Mecha12RumbaoaOsborne/ME405-TERM-PROJECT/Supplemental files/Lab0x00/5 working mostly/log plot.png

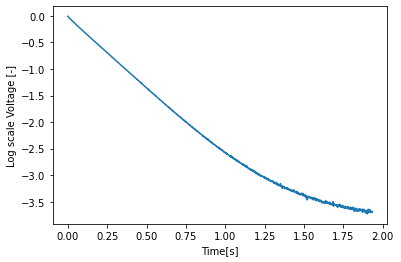
Supplemental files/Lab0x00/5 working mostly/log plot.png
