Mecha12RumbaoaOsborne/ME405-TERM-PROJECT/Supplemental files/Lab0x01/1.2 works/logplotlab1.png

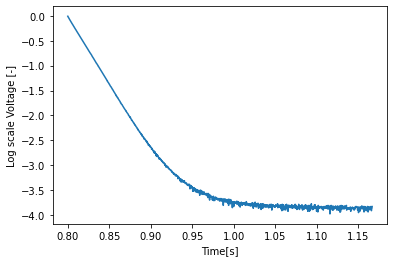
Supplemental files/Lab0x01/1.2 works/logplotlab1.png
