Mecha12RumbaoaOsborne/ME405-TERM-PROJECT/Design Files/PenArmNew.SLDPRT

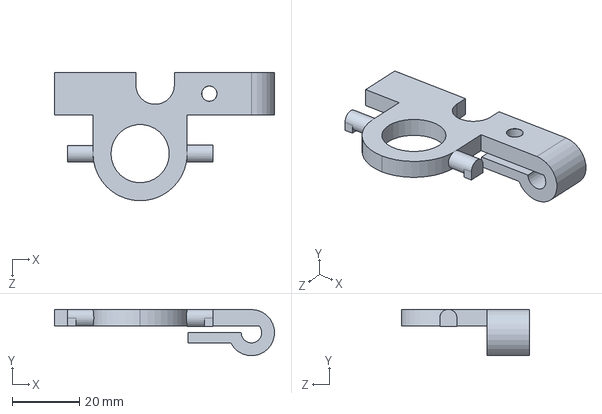
[picture p26: CAD file, 2022-06-10]
Design Files/PenArmNew.SLDPRT
65.3 x 13.8 x 38.1 mm
