Mecha12RumbaoaOsborne/ME405-TERM-PROJECT/Design Files/Radial Gearbox.SLDPRT

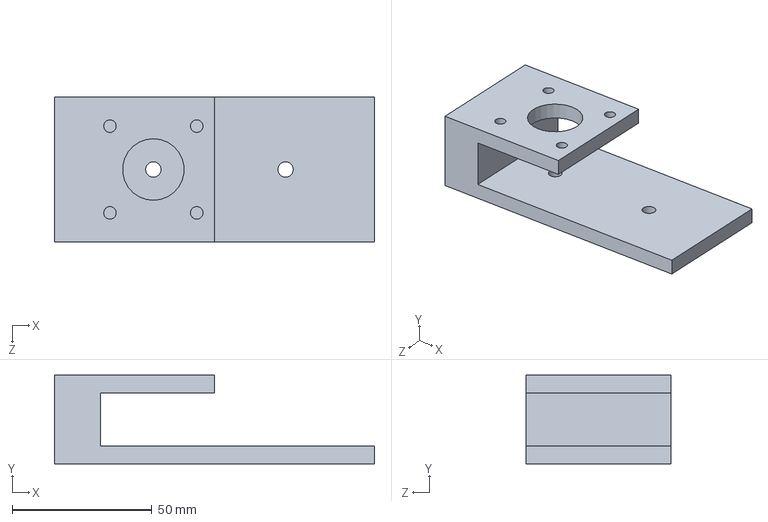
[picture p27: CAD file, 2022-06-10]
Design Files/Radial Gearbox.SLDPRT
114.3 x 31.8 x 51.7 mm
