Mecha12RumbaoaOsborne/ME405-TERM-PROJECT/Design Files/Rollers.SLDPRT

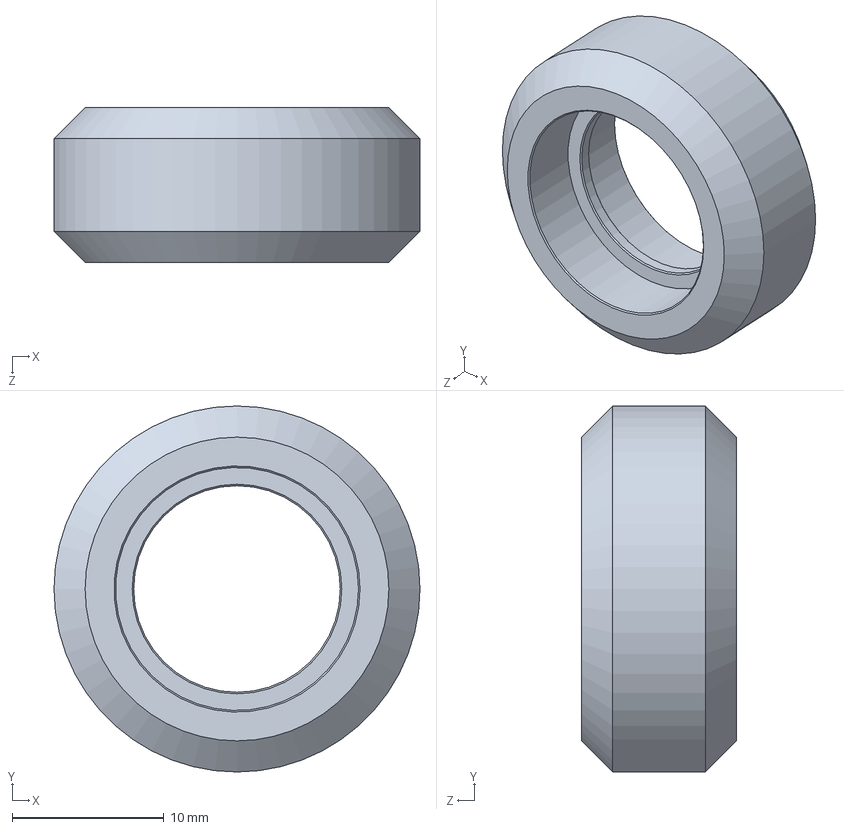
[picture p28: CAD file, 2022-06-10]
Design Files/Rollers.SLDPRT
24.1 x 24.1 x 10.2 mm
