Mecha12RumbaoaOsborne/ME405-TERM-PROJECT/Design Files/Motor Box to go with cage bearing.SLDPRT

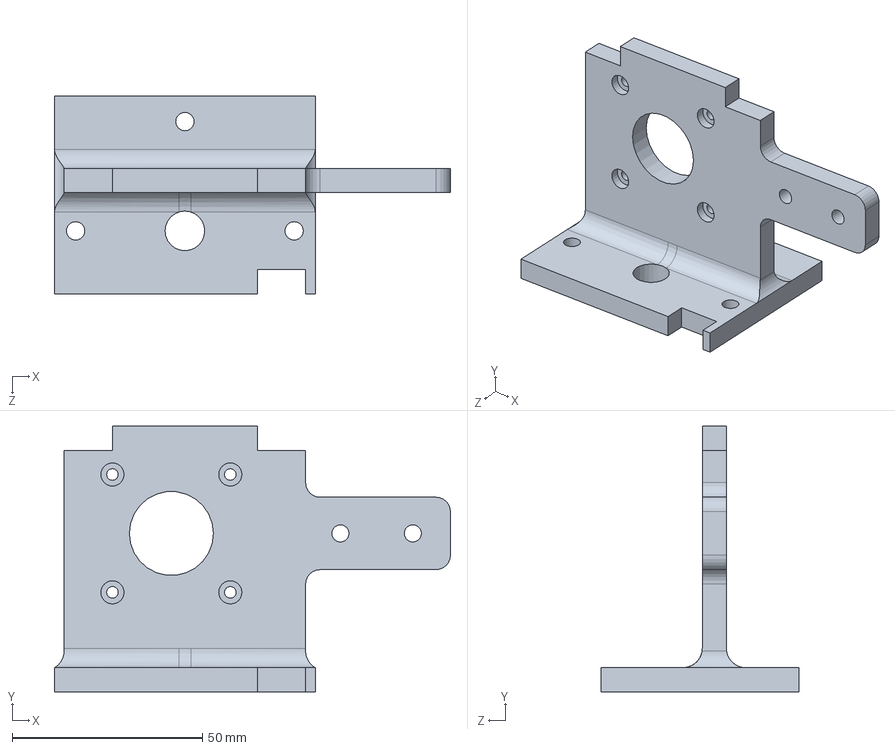
[picture p29: CAD file, 2022-06-10]
Design Files/Motor Box to go with cage bearing.SLDPRT
104.1 x 69.8 x 52.0 mm
