Mecha12RumbaoaOsborne/ME405-TERM-PROJECT/Design Files/spacer bearing.SLDPRT

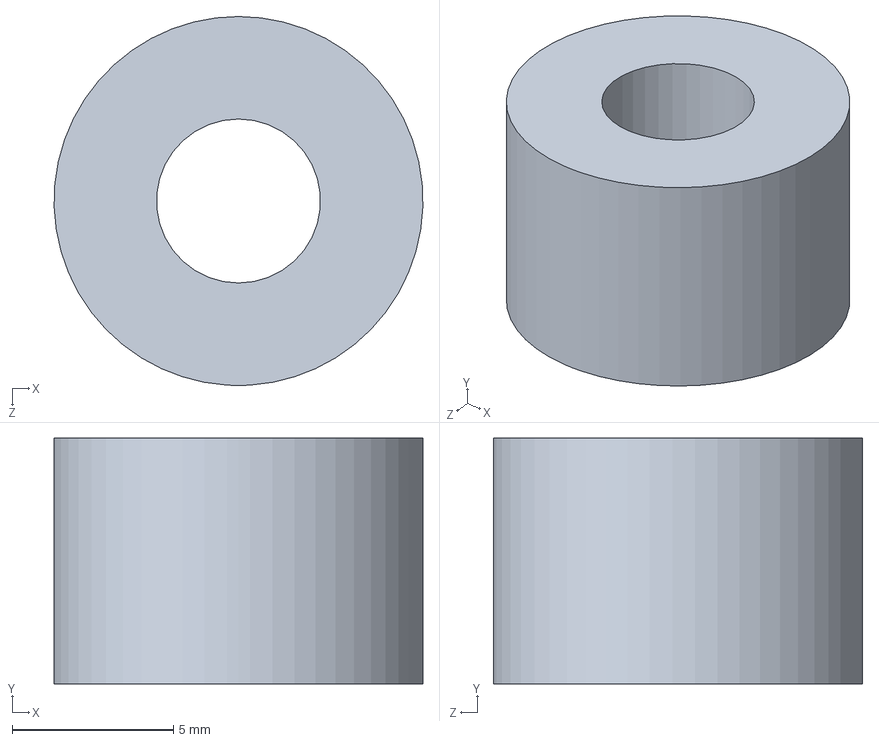
[picture p30: CAD file, 2022-06-10]
Design Files/spacer bearing.SLDPRT
11.4 x 7.62 x 11.4 mm
