Mecha12RumbaoaOsborne/ME405-TERM-PROJECT/Design Files/Motor Box to go with cage.SLDPRT

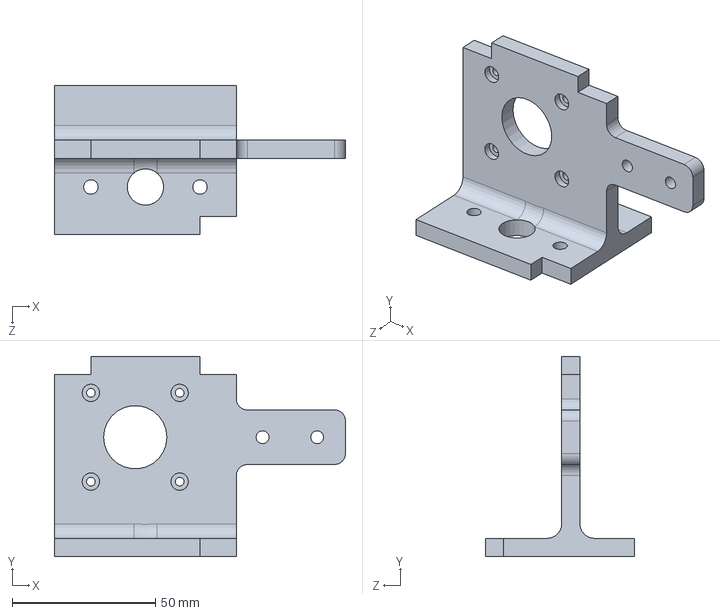
[picture p31: CAD file, 2022-06-10]
Design Files/Motor Box to go with cage.SLDPRT
101.6 x 69.8 x 52.0 mm
