Mecha12RumbaoaOsborne/ME405-TERM-PROJECT/Design Files/DrivenGearWithHoles.SLDPRT

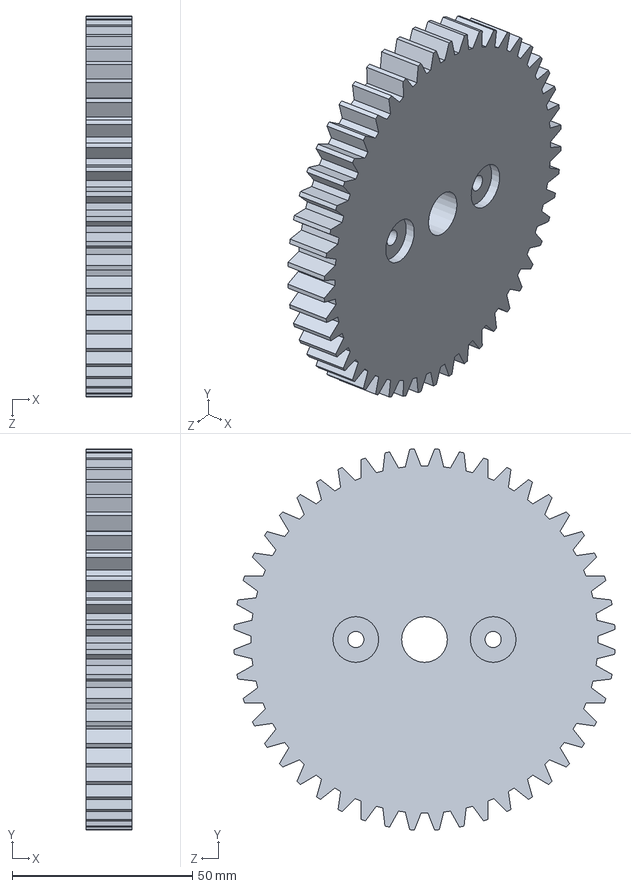
[picture p32: CAD file, 2022-06-10]
Design Files/DrivenGearWithHoles.SLDPRT
12.7 x 105.7 x 105.7 mm
