Mecha12RumbaoaOsborne/ME405-TERM-PROJECT/Design Files/EndPlate Bearing.SLDPRT

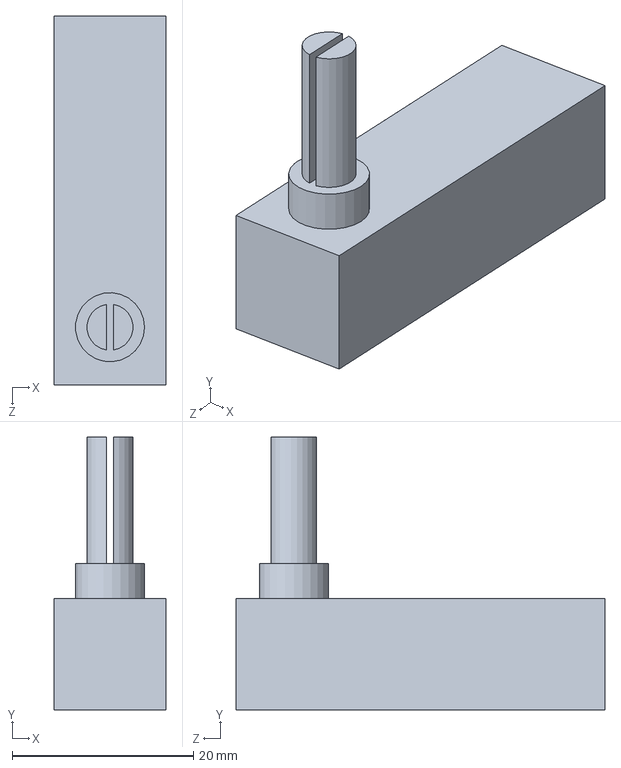
[picture p33: CAD file, 2022-06-10]
Design Files/EndPlate Bearing.SLDPRT
12.3 x 30.1 x 40.6 mm
