Mecha12RumbaoaOsborne/ME405-TERM-PROJECT/Design Files/spur gear_ai1.SLDPRT

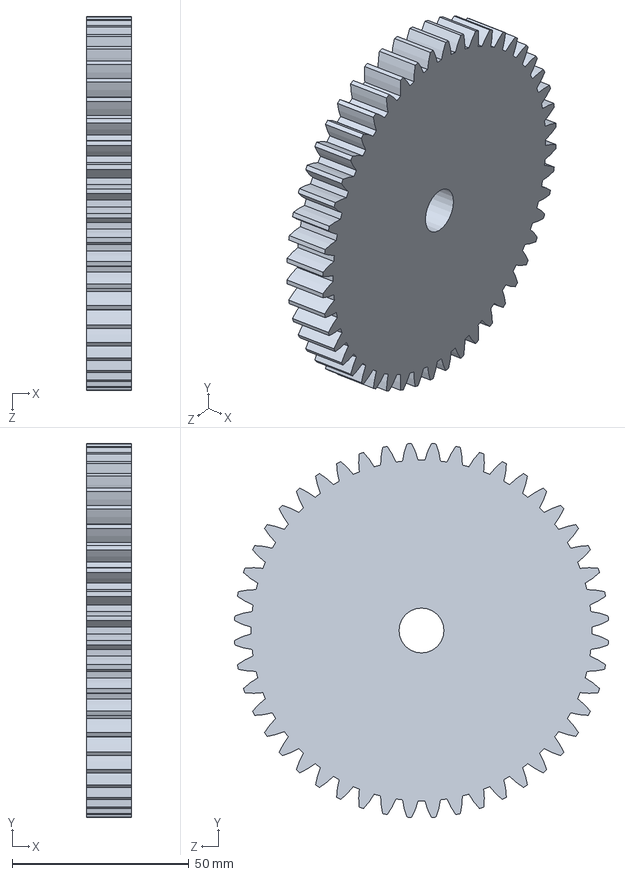
[picture p34: CAD file, 2022-06-10]
Design Files/spur gear_ai1.SLDPRT
12.7 x 105.7 x 105.7 mm
