Mecha12RumbaoaOsborne/ME405-TERM-PROJECT/Design Files/End Plate 2.SLDPRT

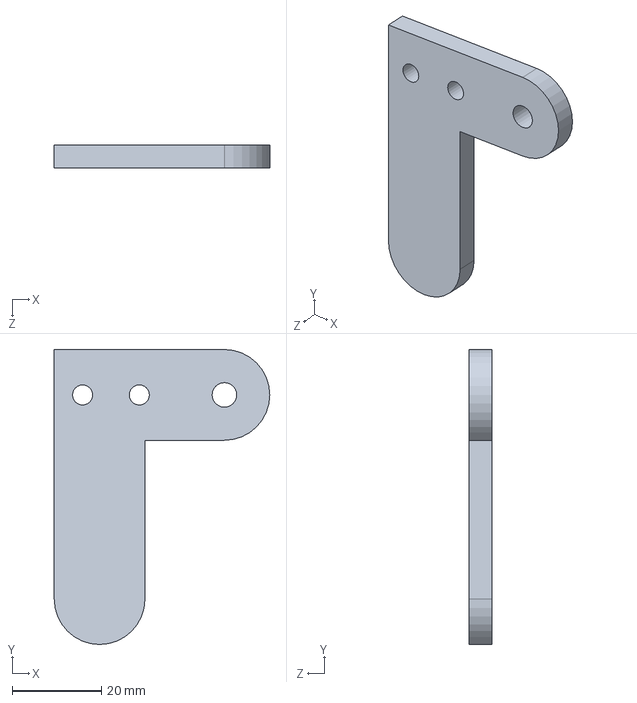
[picture p35: CAD file, 2022-06-10]
Design Files/End Plate 2.SLDPRT
48.3 x 66.0 x 5.08 mm
