Mecha12RumbaoaOsborne/ME405-TERM-PROJECT/Design Files/SmallGear2.SLDPRT

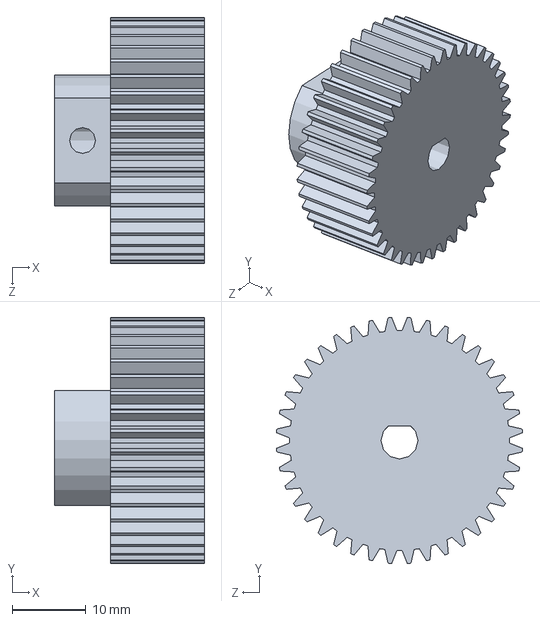
[picture p36: CAD file, 2022-06-10]
Design Files/SmallGear2.SLDPRT
20.3 x 33.3 x 33.3 mm
