Mecha12RumbaoaOsborne/ME405-TERM-PROJECT/Design Files/Carriage Plate.SLDPRT

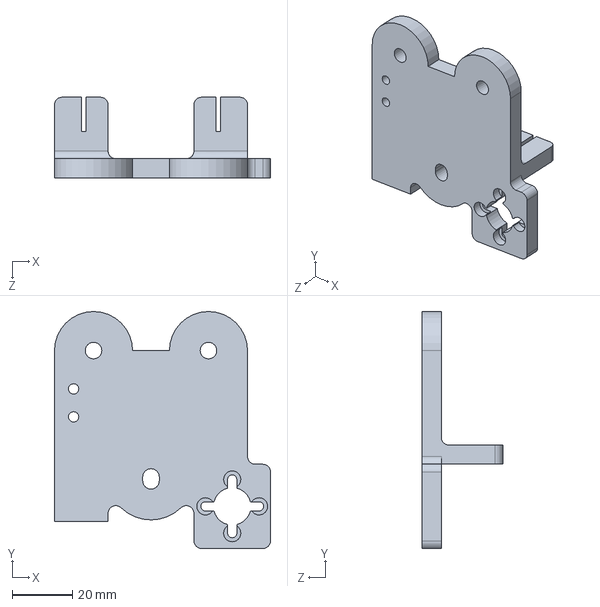
[picture p37: CAD file, 2022-06-10]
Design Files/Carriage Plate.SLDPRT
71.6 x 78.6 x 26.7 mm
