Mecha12RumbaoaOsborne/ME405-TERM-PROJECT/Design Files/Gear1 hub.SLDPRT

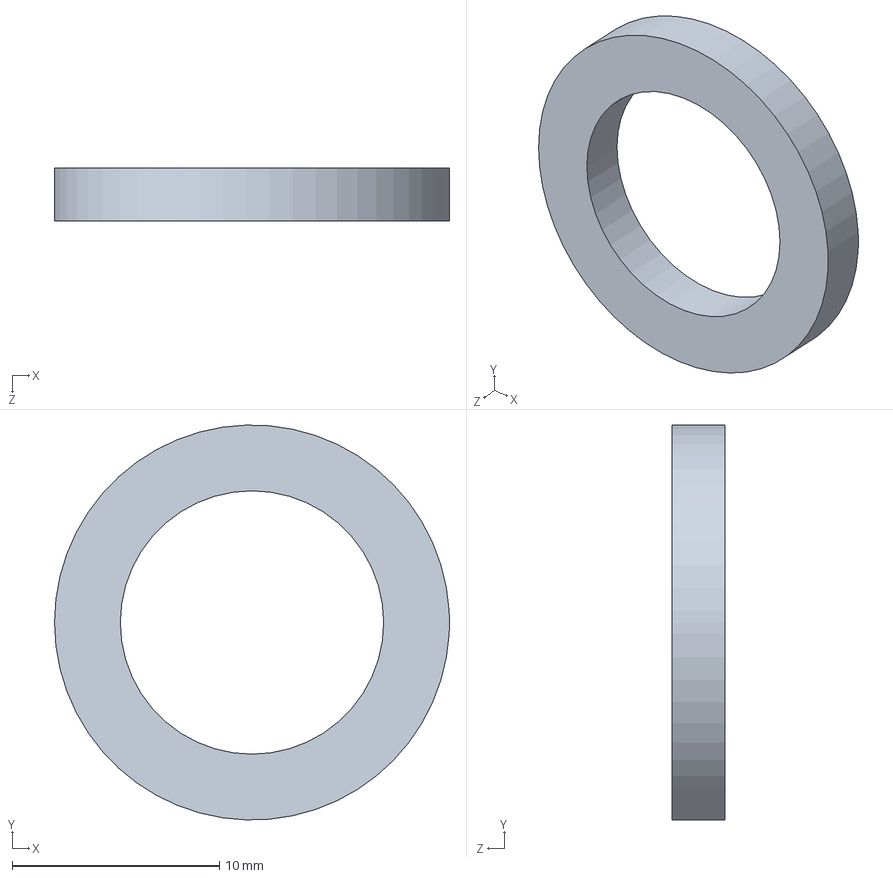
[picture p38: CAD file, 2022-06-10]
Design Files/Gear1 hub.SLDPRT
19.1 x 19.0 x 2.54 mm
