Mecha12RumbaoaOsborne/ME405-TERM-PROJECT/Design Files/spur gear_ai2.SLDPRT

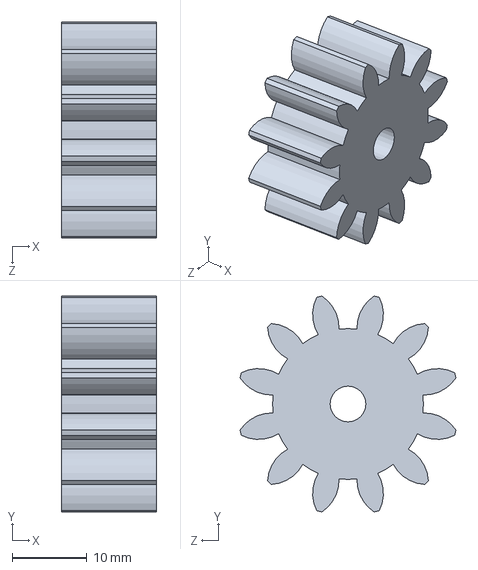
[picture p39: CAD file, 2022-06-10]
Design Files/spur gear_ai2.SLDPRT
12.7 x 28.8 x 28.8 mm
