Mecha12RumbaoaOsborne/ME405-TERM-PROJECT/Design Files/SpurGearBig.SLDPRT

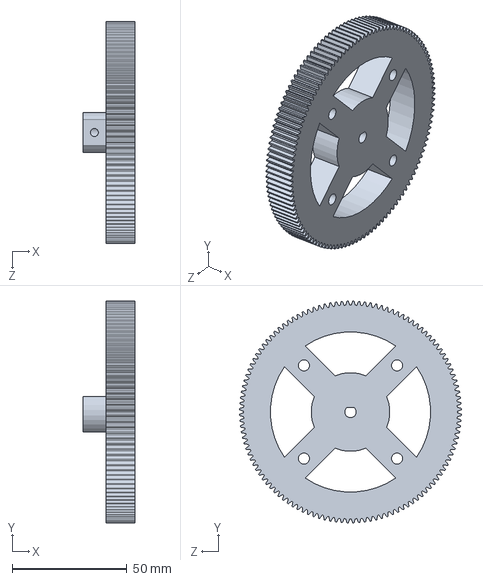
[picture p40: CAD file, 2022-06-10]
Design Files/SpurGearBig.SLDPRT
22.9 x 96.8 x 96.8 mm
