Mecha12RumbaoaOsborne/ME405-TERM-PROJECT/Design Files/Roller bushing.SLDPRT

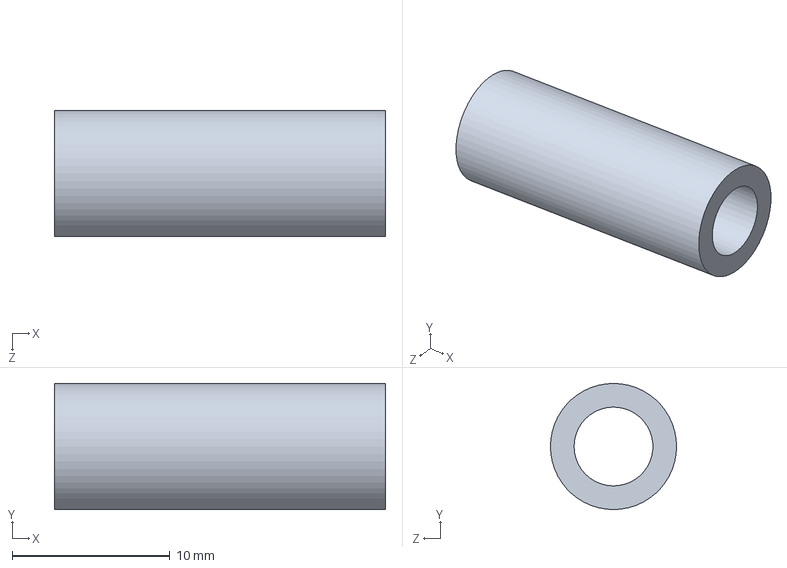
[picture p41: CAD file, 2022-06-10]
Design Files/Roller bushing.SLDPRT
21.0 x 8.00 x 8.00 mm
