Mecha12RumbaoaOsborne/ME405-TERM-PROJECT/Design Files/Baseplate spacer.SLDPRT

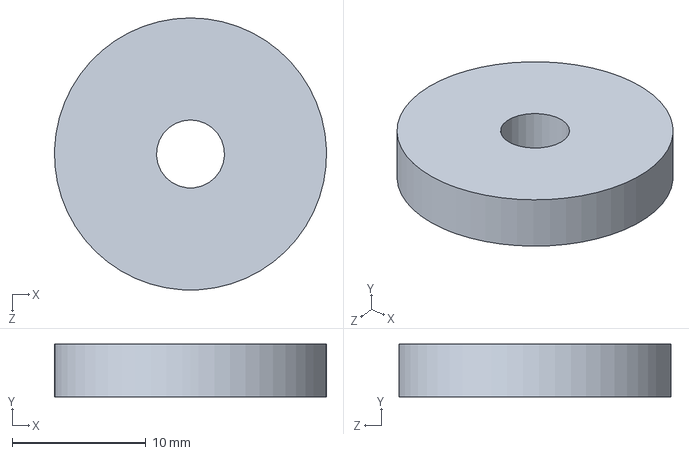
[picture p42: CAD file, 2022-06-10]
Design Files/Baseplate spacer.SLDPRT
20.3 x 3.94 x 20.3 mm
