Mecha12RumbaoaOsborne/ME405-TERM-PROJECT/Design Files/Spring Pegs.SLDPRT

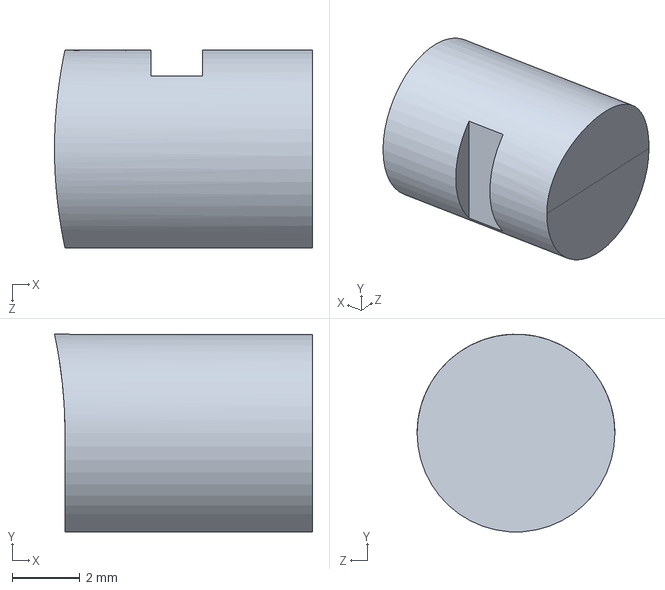
[picture p43: CAD file, 2022-06-10]
Design Files/Spring Pegs.SLDPRT
7.62 x 5.83 x 5.84 mm
