Mecha12RumbaoaOsborne/ME405-TERM-PROJECT/Design Files/BearingCenter.SLDPRT

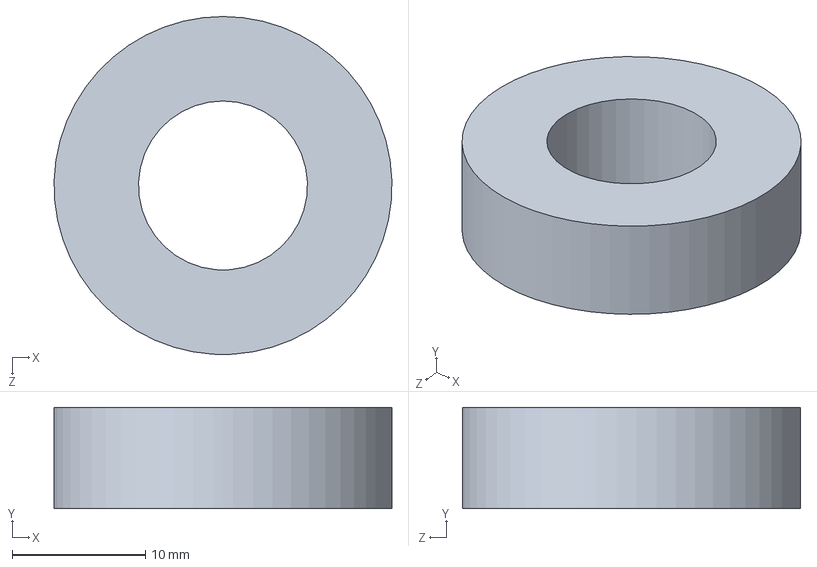
[picture p44: CAD file, 2022-06-10]
Design Files/BearingCenter.SLDPRT
25.4 x 7.62 x 25.4 mm
