Mecha12RumbaoaOsborne/ME405-TERM-PROJECT/Design Files/baseplate without axel guard.SLDPRT

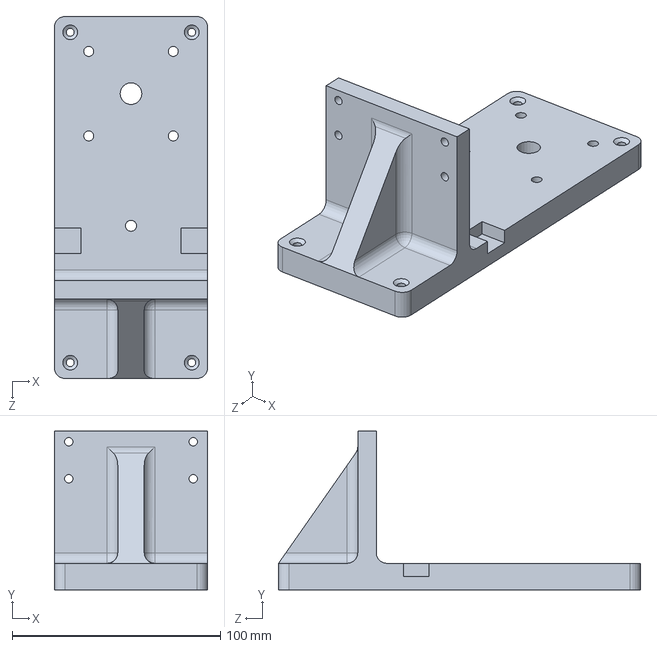
[picture p45: CAD file, 2022-06-10]
Design Files/baseplate without axel guard.SLDPRT
73.7 x 76.2 x 174.0 mm
