Mecha12RumbaoaOsborne/ME405-TERM-PROJECT/Design Files/2020-2 profile.SLDPRT

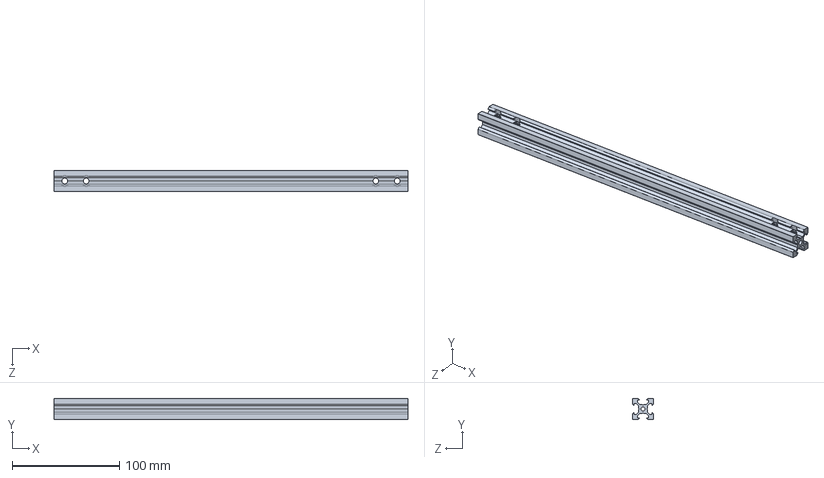
[picture p46: CAD file, 2022-06-10]
Design Files/2020-2 profile.SLDPRT
330.0 x 20.0 x 20.0 mm
