Mecha12RumbaoaOsborne/ME405-TERM-PROJECT/Design Files/Bearingtop.SLDPRT

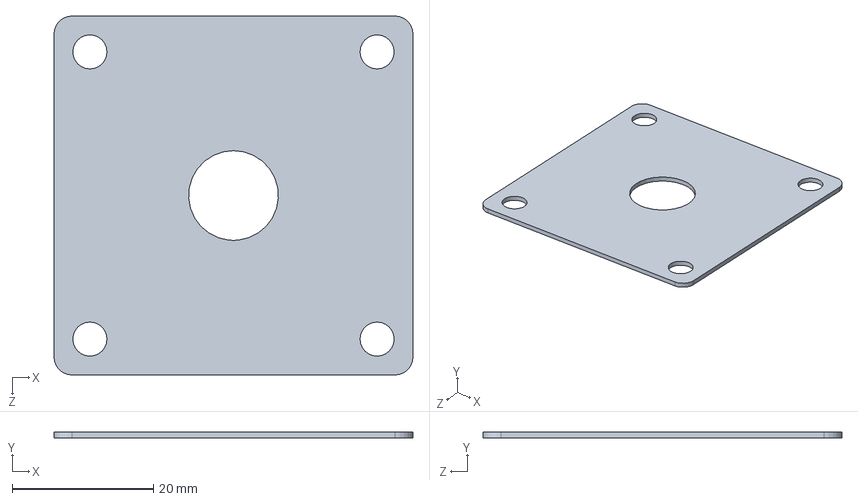
[picture p47: CAD file, 2022-06-10]
Design Files/Bearingtop.SLDPRT
50.8 x 0.889 x 50.8 mm
