Mecha12RumbaoaOsborne/ME405-TERM-PROJECT/Design Files/BaseArm gaurd.SLDPRT

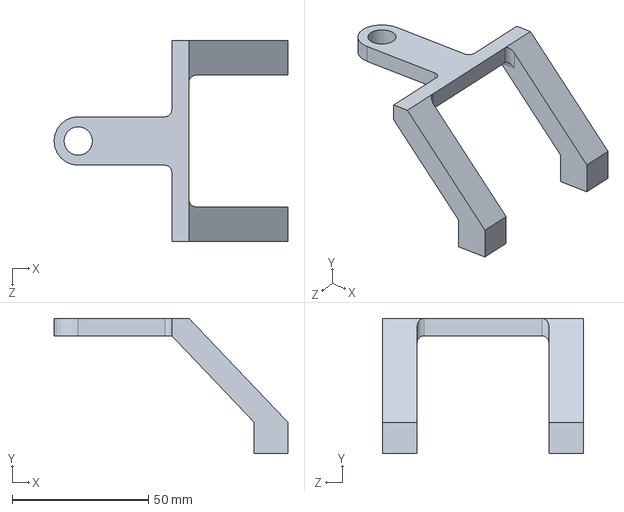
[picture p48: CAD file, 2022-06-10]
Design Files/BaseArm gaurd.SLDPRT
85.8 x 49.5 x 73.7 mm
