Mecha12RumbaoaOsborne/ME405-TERM-PROJECT/Design Files/Carriage Plate unbent.SLDPRT

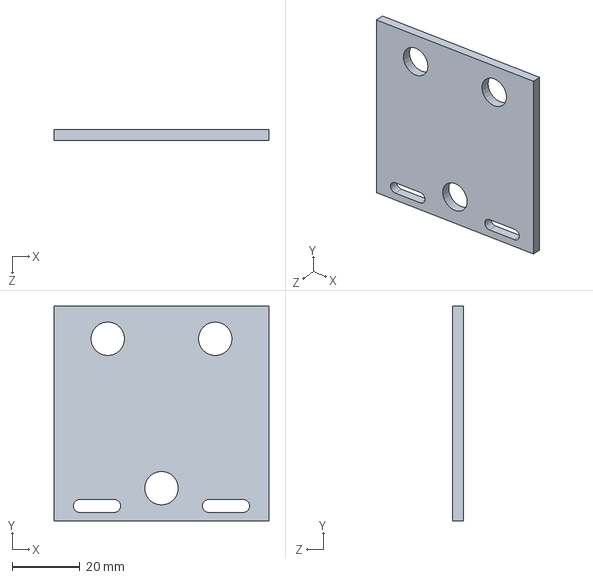
[picture p49: CAD file, 2022-06-10]
Design Files/Carriage Plate unbent.SLDPRT
63.5 x 63.5 x 3.17 mm
