Mecha12RumbaoaOsborne/ME405-TERM-PROJECT/Design Files/SpringEnd.SLDPRT

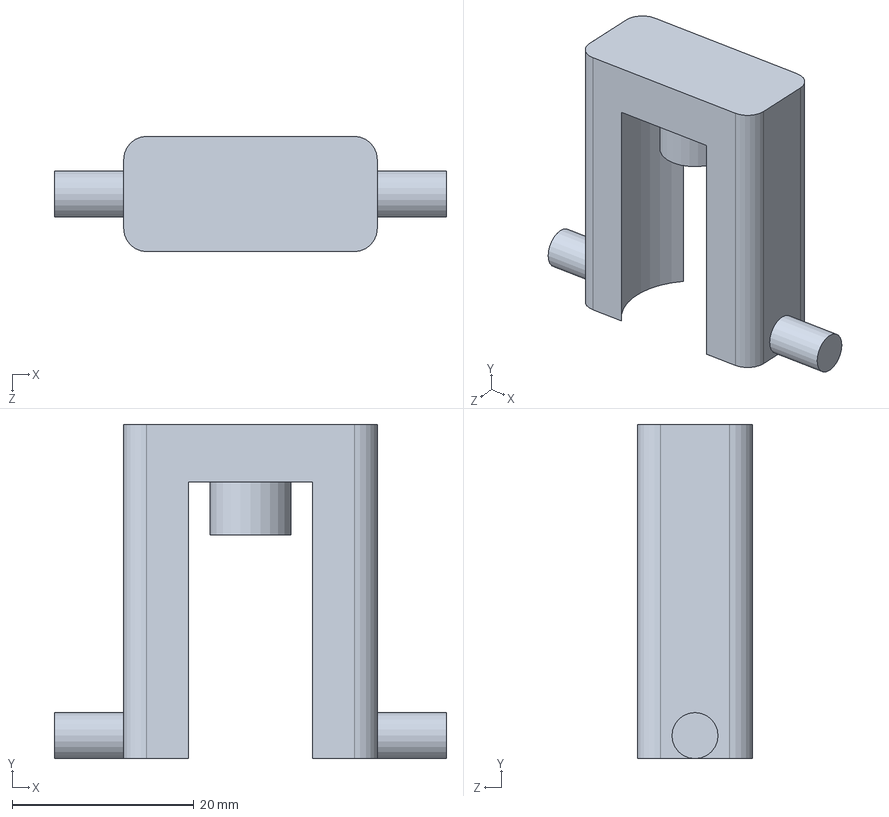
[picture p50: CAD file, 2022-06-10]
Design Files/SpringEnd.SLDPRT
43.2 x 36.8 x 12.7 mm
