Mecha12RumbaoaOsborne/ME405-TERM-PROJECT/Design Files/X belt.SLDPRT

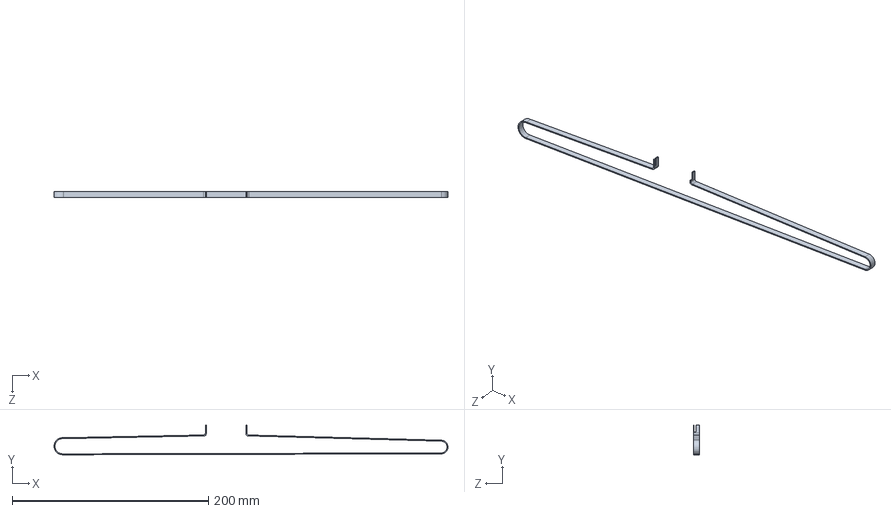
[picture p51: CAD file, 2022-06-10]
Design Files/X belt.SLDPRT
401.8 x 30.2 x 6.00 mm
