Mecha12RumbaoaOsborne/ME405-TERM-PROJECT/Design Files/baseplate2.SLDPRT

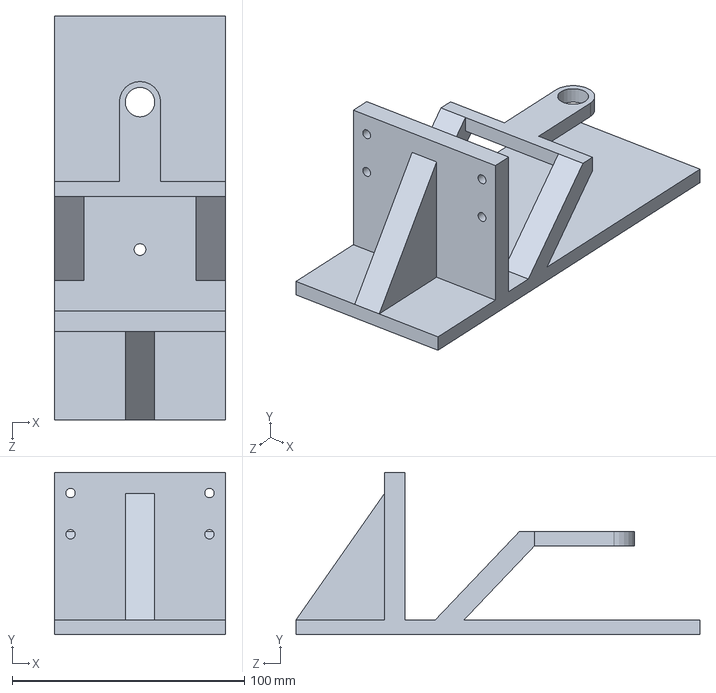
[picture p52: CAD file, 2022-06-10]
Design Files/baseplate2.SLDPRT
73.7 x 69.8 x 174.0 mm
