Mecha12RumbaoaOsborne/ME405-TERM-PROJECT/Design Files/NEW END BEAM.SLDPRT

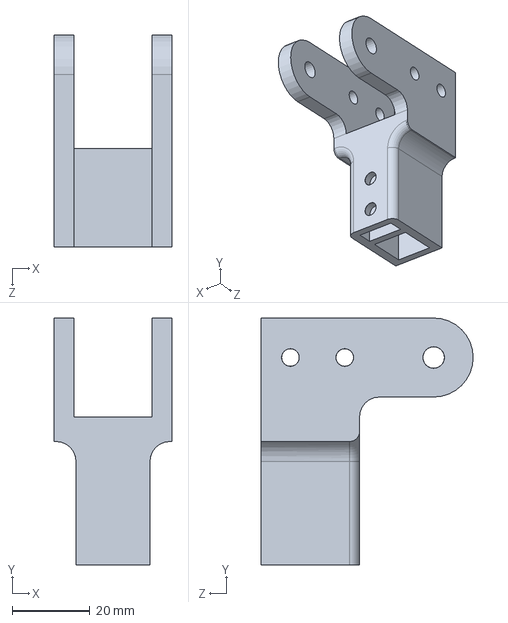
[picture p53: CAD file, 2022-06-10]
Design Files/NEW END BEAM.SLDPRT
30.2 x 63.5 x 54.6 mm
