Mecha12RumbaoaOsborne/ME405-TERM-PROJECT/Design Files/spacer end.SLDPRT

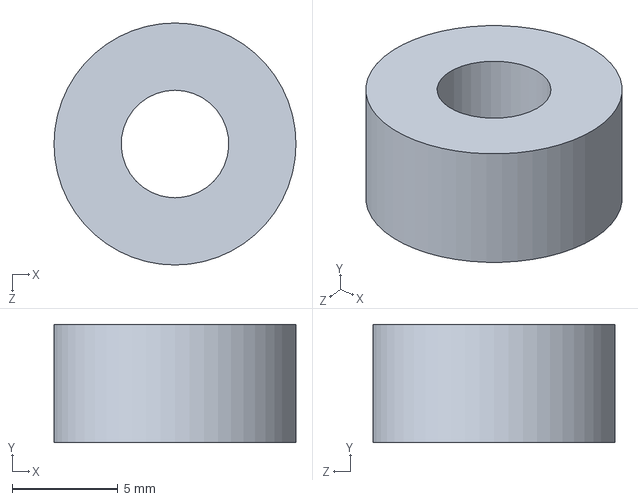
[picture p54: CAD file, 2022-06-10]
Design Files/spacer end.SLDPRT
11.4 x 5.59 x 11.4 mm
