Mecha12RumbaoaOsborne/ME405-TERM-PROJECT/Design Files/SmallGear.SLDPRT

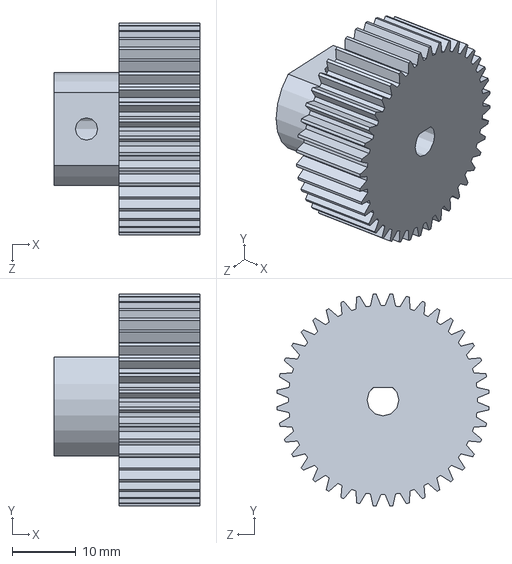
[picture p55: CAD file, 2022-06-10]
Design Files/SmallGear.SLDPRT
22.9 x 33.3 x 33.3 mm
