Mecha12RumbaoaOsborne/ME405-TERM-PROJECT/Design Files/E plate.SLDPRT

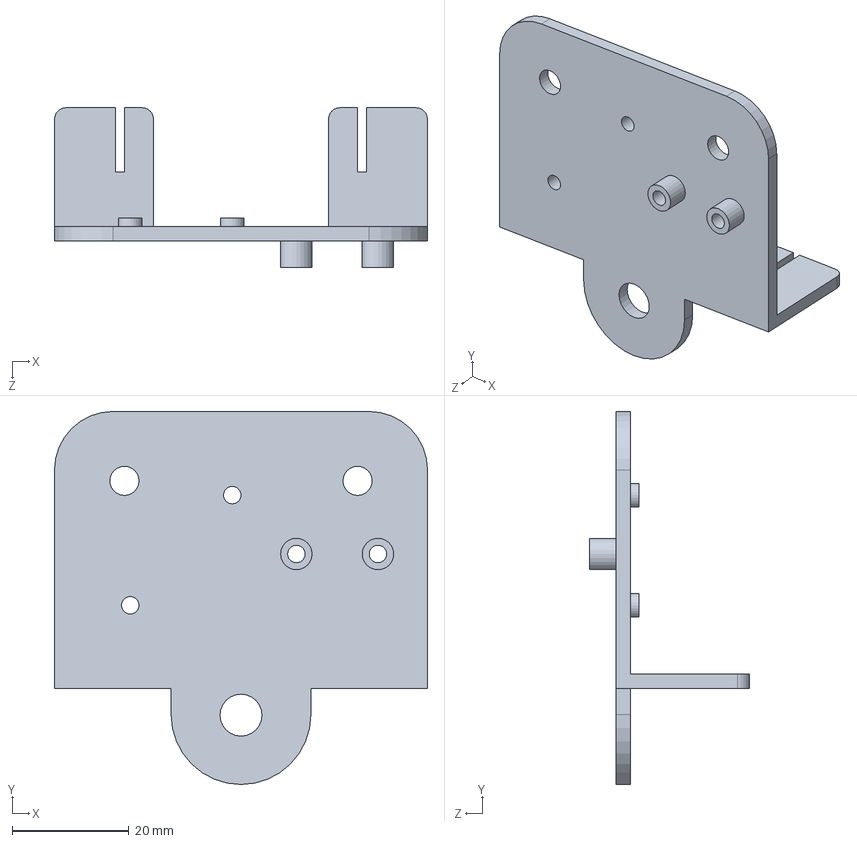
[picture p56: CAD file, 2022-06-10]
Design Files/E plate.SLDPRT
64.0 x 64.0 x 27.4 mm
