Mecha12RumbaoaOsborne/ME405-TERM-PROJECT/Design Files/DrivingGear.SLDPRT

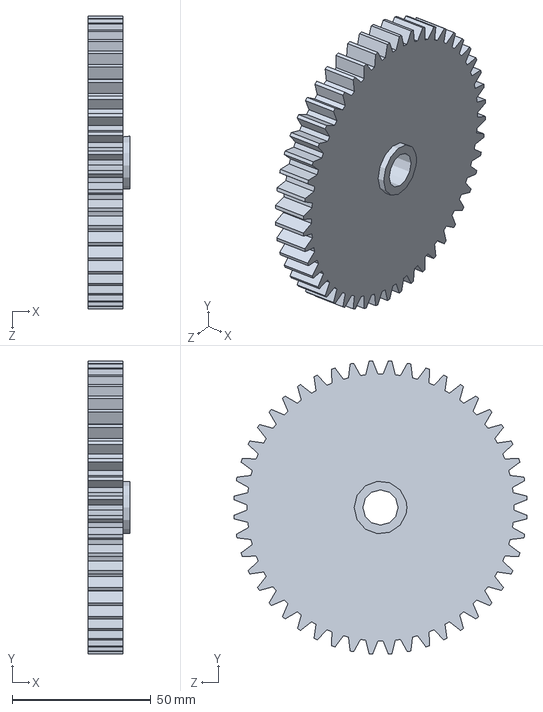
[picture p57: CAD file, 2022-06-10]
Design Files/DrivingGear.SLDPRT
15.2 x 105.7 x 105.7 mm
