Mecha12RumbaoaOsborne/ME405-TERM-PROJECT/Design Files/Gear2 hub.SLDPRT

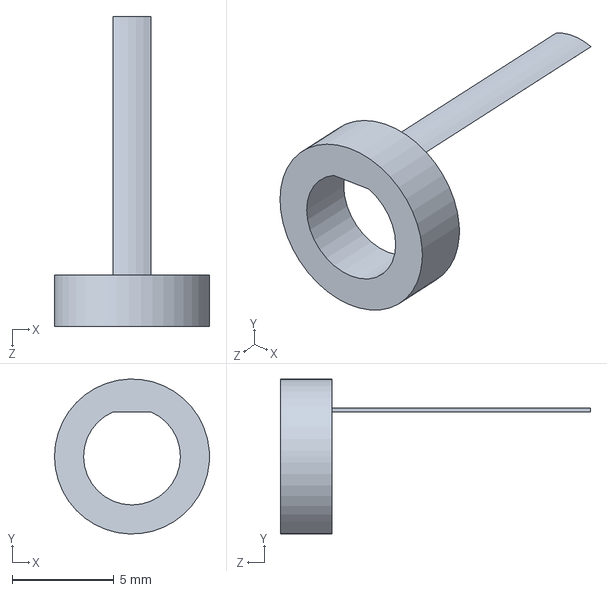
[picture p58: CAD file, 2022-06-10]
Design Files/Gear2 hub.SLDPRT
7.62 x 7.61 x 15.2 mm
