Mecha12RumbaoaOsborne/ME405-TERM-PROJECT/Supplemental files/Lab0x00/5 working mostly/PCScript.py

import serial, math
from matplotlib import pyplot

#Measured res and cap
#R = 102.3e3
#C = 3.24e-6

K = 3.3/4000
T = 1/1000
m=1500
raw_data = m*[0]
time_vals = m*[0]
adc_vals = m*[0]

#Opens COM6 to read the data written to uart2 from pyboard
with serial.Serial('COM6', 115200) as uart2:
    uart2.flush()
    
    #Processes raw data to get time and adc values into previously defined lists
    for idx, line in enumerate(raw_data):
        raw_data = bytes.decode(uart2.readline())
        time_vals[idx], adc_vals[idx] = raw_data.strip('\r\n').split(',')
        
    
    #Converts units from ms to s and from adc to V 
    time_sec = [float(item)*T for item in time_vals]
    adc_volts = [float(item)*K for item in adc_vals]
    log_volts = [math.log((3.3-float(item))/3.3) for item in adc_volts]
    
    #Prints the processed data on console as two columns
    for time_val, adc_val in zip(time_sec, adc_volts):
        print(round(float(time_val), 3),round(float(adc_val), 3))
    
    #Calculates rise/run (slope) of linear region of log data
    slope = round((float(log_volts[400])-float(time_vals[0]))/(float(time_sec[400])-float(time_sec[0])), 4)    
    
    #Step Response plot
    pyplot.figure(1)
    pyplot.plot(time_sec, adc_volts)
    pyplot.xlabel('Time [s]')
    pyplot.ylabel('Vout [V]')
    
    #Log plot
    pyplot.figure(2)
    pyplot.plot(time_sec,log_volts)#.annotate(f'Slope:{slope}', xy = (0.25,-2.5), xytext =(0.25,-2.5))
    pyplot.xlabel('Time[s]')
    pyplot.ylabel('Log scale Voltage [-]')
    
    #Wasn't able to print the slope onto the figure so jut printing it on console
    print('')
    print(f'The slope of the log plot is: {slope}')
                
        #     else:
        #         pass
        # except KeyboardInterrupt:
        #     break
