Mecha12RumbaoaOsborne/ME405-TERM-PROJECT/Supplemental files/Lab0x00/5 working mostly/boot.py

# boot.py -- run on boot to configure USB and filesystem
# Put app code in main.py

import machine
import pyb
#from micropython import alloc_emergency_exception_buf
pyb.country('US') # ISO 3166-1 Alpha-2 code, eg US, GB, DE, AU
#pyb.main('main.py') # main script to run after this one
#pyb.usb_mode('VCP+MSC') # act as a serial and a storage device
#pyb.usb_mode('VCP+HID') # act as a serial device and a mouse
#alloc_emergency_exception_buf(100)
pyb.repl_uart(None)
